bastlirna/lora-probulator/photo/photo1.jpg

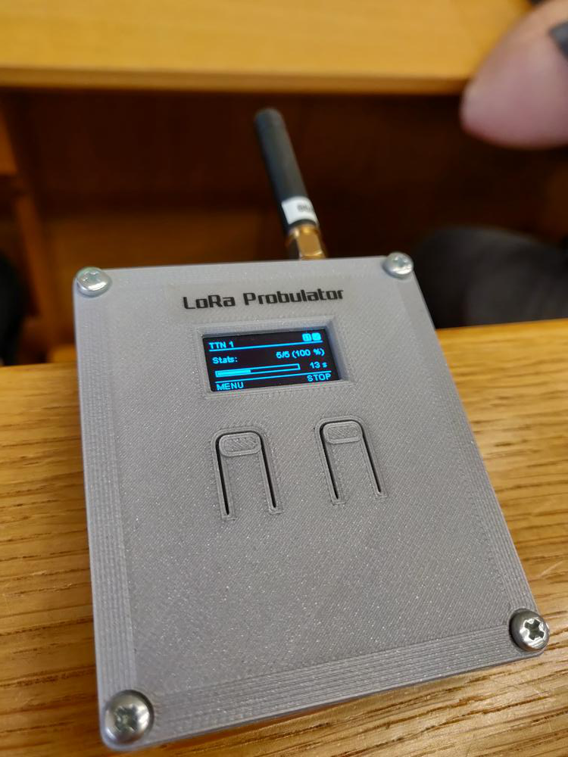
photo/photo1.jpg
