bastlirna/lora-probulator/photo/screen-mirror.gif

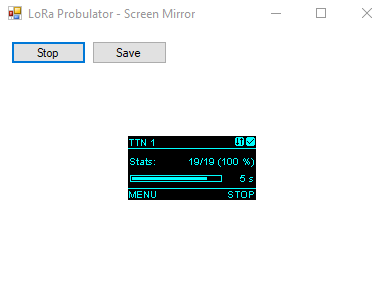
photo/screen-mirror.gif
