bastlirna/lora-probulator/hw/enclosure/btm-panel.scad

use <_parts.scad>
use <_utils.scad>
include <_params.scad>

module btm_panel() {

    panel();  
}



btm_panel();
